leafai-io/leaf-node-v3.x/firmware/src/runtime/RuntimeConfig.cpp

#include "RuntimeConfig.h"
#include <Preferences.h>
#include "../LeafNodeTypes.h"
#include "config.h"

// Forward declaration helper functions for LogLevel conversion
String logLevelToString(LogLevel level) {
    switch (level) {
        case LogLevel::TRACE:   return "TRACE";
        case LogLevel::DEBUG:   return "DEBUG";
        case LogLevel::INFO:    return "INFO";
        case LogLevel::WARNING: return "WARNING";
        case LogLevel::ERROR:   return "ERROR";
        case LogLevel::FATAL:   return "FATAL";
        default:               return "INFO";
    }
}

LogLevel stringToLogLevel(const String& levelStr) {
    String upper = levelStr;
    upper.toUpperCase();
    
    if (upper == "TRACE")   return LogLevel::TRACE;
    if (upper == "DEBUG")   return LogLevel::DEBUG;
    if (upper == "INFO")    return LogLevel::INFO;
    if (upper == "WARNING" || upper == "WARN") return LogLevel::WARNING;
    if (upper == "ERROR")   return LogLevel::ERROR;
    if (upper == "FATAL")   return LogLevel::FATAL;
    
    return LogLevel::INFO; // Default
}

// Helper functions for SensorProfile conversion
String RuntimeConfig::sensorProfileToString(SensorProfile profile) const {
    switch (profile) {
        case SensorProfile::NONE:       return "NONE";
        case SensorProfile::SLT5007:    return "SLT5007";
        case SensorProfile::SHT31:      return "SHT31";
        case SensorProfile::CWTPSS:     return "CWTPSS";
        case SensorProfile::LEAFTHSN:   return "LEAFTHSN";
        case SensorProfile::CWTSOILTHS: return "CWTSOILTHS";
        case SensorProfile::TEROS12:    return "TEROS12";
        case SensorProfile::EZOPH:      return "EZOPH";
        case SensorProfile::EZOEC:      return "EZOEC";
        case SensorProfile::DS18B20:    return "DS18B20";
        case SensorProfile::CWTTHXXS:   return "CWTTHXXS";
        default:                        return "UNKNOWN";
    }
}

SensorProfile RuntimeConfig::stringToSensorProfile(const String& profileStr) const {
    String upper = profileStr;
    upper.toUpperCase();
    
    if (upper == "NONE")       return SensorProfile::NONE;
    if (upper == "SLT5007")    return SensorProfile::SLT5007;
    if (upper == "SHT31")      return SensorProfile::SHT31;
    if (upper == "CWTPSS")     return SensorProfile::CWTPSS;
    if (upper == "LEAFTHSN")   return SensorProfile::LEAFTHSN;
    if (upper == "CWTSOILTHS") return SensorProfile::CWTSOILTHS;
    if (upper == "TEROS12")    return SensorProfile::TEROS12;
    if (upper == "EZOPH")      return SensorProfile::EZOPH;
    if (upper == "EZOEC")      return SensorProfile::EZOEC;
    if (upper == "DS18B20")    return SensorProfile::DS18B20;
    if (upper == "CWTTHXXS")   return SensorProfile::CWTTHXXS;
    
    return SensorProfile::NONE; // Default
}

RuntimeConfig::RuntimeConfig() : configDoc_(2048), loaded_(false), dirty_(false), 
                                 setupStartTime_(0), setupTimeoutActive_(false) {
    setDefaults();
}

RuntimeConfig::~RuntimeConfig() {
    // Don't auto-save in destructor to avoid unnecessary flash writes
    // Config is explicitly saved after actual changes via command handlers
    if (dirty_) {
        Serial.println("[WARNING] RuntimeConfig destructed with unsaved changes (dirty flag set)");
    }
}

bool RuntimeConfig::load() {
    if (!loadFromPreferences()) {
        setDefaults();
        loadSerialNumberFromFactory(); // Load serial number from factory partition
        return false;
    }
    
    // Always try to load serial number from factory, even if config exists
    loadSerialNumberFromFactory();
    
    // Always update firmware version to current version after loading from NVS
    // This ensures the version in config matches the actual running firmware
    configDoc_["device"]["version"] = FIRMWARE_VERSION;
    
    loaded_ = true;
    dirty_ = false;
    return validate();
}

bool RuntimeConfig::save() {
    if (!saveToPreferences()) {
        return false;
    }
    
    dirty_ = false;
    return true;
}

void RuntimeConfig::resetToDefaults() {
    setDefaults();
    dirty_ = true;
}

bool RuntimeConfig::validate() const {
    // Validate device name
    String deviceName = getDeviceName();
    if (deviceName.length() == 0 || deviceName.length() > MAX_DEVICE_NAME_LENGTH) {
        return false;
    }
    
    // Validate serial number
    String serialNumber = getSerialNumber();
    if (serialNumber.length() == 0 || serialNumber.length() > MAX_SERIAL_NUMBER_LENGTH) {
        return false;
    }
    
    // Validate heartbeat interval
    uint32_t interval = getHeartbeatInterval();
    if (interval < 1000 || interval > 300000) { // 1 second to 5 minutes
        return false;
    }
    
    return true;
}

bool RuntimeConfig::setFromJson(const DynamicJsonDocument& json) {
    configDoc_ = json;
    dirty_ = true;
    return validate();
}

String RuntimeConfig::getDeviceName() const {
    return configDoc_["device"]["name"] | generateDefaultDeviceName();
}

String RuntimeConfig::getSerialNumber() const {
    return configDoc_["device"]["serial_number"] | "UNKNOWN";
}

String RuntimeConfig::getWiFiSSID() const {
    return configDoc_["wifi"]["ssid"] | "";
}

String RuntimeConfig::getWiFiPassword() const {
    return configDoc_["wifi"]["password"] | "";
}

String RuntimeConfig::getBLEKey() const {
    return configDoc_["ble"]["key"] | "DEFAULT_KEY";
}

LogLevel RuntimeConfig::getLogLevel() const {
    String levelStr = configDoc_["logging"]["level"] | "INFO";
    return stringToLogLevel(levelStr);
}

uint32_t RuntimeConfig::getHeartbeatInterval() const {
    return configDoc_["system"]["heartbeat_interval"] | HEARTBEAT_INTERVAL;
}

bool RuntimeConfig::isDebugMode() const {
    return configDoc_["system"]["debug_mode"] | false;
}

bool RuntimeConfig::hasWiFiCredentials() const {
    String ssid = getWiFiSSID();
    String password = getWiFiPassword();
    return !ssid.isEmpty() && !password.isEmpty();
}

bool RuntimeConfig::hasValidSensorConfiguration() const {
    // Fresh device (not loaded from storage) needs Factory Mode configuration
    // Even if defaults set sensor to NONE, user must explicitly configure it
    if (!loaded_) {
        return false;
    }
    
    // Configuration was loaded from storage - check if sensor profile is set
    // NONE is a valid configuration (for devices without sensors)
    if (!configDoc_["sensor"]["profile"].is<String>()) {
        return false;
    }
    String profile = configDoc_["sensor"]["profile"] | "";
    return !profile.isEmpty();
}

bool RuntimeConfig::isFactoryMode() const {
    // Factory Mode wenn die essentiellen Komponenten fehlen:
    // - Serial Number (sollte aus Factory Partition kommen)
    // - MQTT Configuration (Server-Verbindung)
    // - Sensor Configuration (welcher Sensor ist angeschlossen, NONE ist erlaubt)
    // WiFi ist OPTIONAL - kann später über BLE konfiguriert werden
    
    bool hasSerial = !getSerialNumber().isEmpty() && getSerialNumber() != "UNKNOWN";
    bool hasValidSensor = hasValidSensorConfiguration();
    
    // Factory Mode wenn Serial ODER MQTT ODER Sensor fehlt
    return !hasSerial || !hasMQTTCredentials() || !hasValidSensor;
}

void RuntimeConfig::setDeviceName(const String& name) {
    configDoc_["device"]["name"] = name;
    dirty_ = true;
}

void RuntimeConfig::setSerialNumber(const String& serialNumber) {
    configDoc_["device"]["serial_number"] = serialNumber;
    dirty_ = true;
}

void RuntimeConfig::setWiFiCredentials(const String& ssid, const String& password) {
    // Create temporary copies to ensure proper memory allocation
    String tempSsid = ssid;
    String tempPassword = password;
    configDoc_["wifi"]["ssid"] = tempSsid;
    configDoc_["wifi"]["password"] = tempPassword;
    dirty_ = true;
}

void RuntimeConfig::setBLEKey(const String& bleKey) {
    configDoc_["ble"]["key"] = bleKey;
    dirty_ = true;
}

void RuntimeConfig::setLogLevel(LogLevel level) {
    configDoc_["logging"]["level"] = logLevelToString(level);
    dirty_ = true;
}

void RuntimeConfig::setHeartbeatInterval(uint32_t interval) {
    configDoc_["system"]["heartbeat_interval"] = interval;
    dirty_ = true;
}

void RuntimeConfig::setDebugMode(bool enabled) {
    configDoc_["system"]["debug_mode"] = enabled;
    dirty_ = true;
}

void RuntimeConfig::setDefaults() {
    configDoc_.clear();
    
    // Device configuration
    configDoc_["device"]["name"] = generateDefaultDeviceName();
    configDoc_["device"]["type"] = "leaf-node";
    configDoc_["device"]["version"] = FIRMWARE_VERSION;
    configDoc_["device"]["setup_complete"] = false; // Device needs initial setup
    
    // System configuration
    configDoc_["system"]["heartbeat_interval"] = HEARTBEAT_INTERVAL;
    configDoc_["system"]["debug_mode"] = false;
    configDoc_["system"]["auto_update"] = true;
    
    // Logging configuration
    configDoc_["logging"]["level"] = "INFO";
    configDoc_["logging"]["enable_serial"] = true;
    configDoc_["logging"]["enable_timestamp"] = true;
    
    // WiFi configuration (empty by default)
    configDoc_["wifi"]["ssid"] = "";
    configDoc_["wifi"]["password"] = "";
    configDoc_["wifi"]["auto_connect"] = true;
    
    // BLE configuration
    configDoc_["ble"]["key"] = "LeafNode2025";
    configDoc_["ble"]["device_name"] = getDeviceName();
    configDoc_["ble"]["enabled"] = true;
    
    // MQTT configuration (empty by default, set by factory firmware)
    configDoc_["mqtt"]["server"] = "";
    configDoc_["mqtt"]["port"] = 1883;
    configDoc_["mqtt"]["username"] = "";
    configDoc_["mqtt"]["password"] = "";
    configDoc_["mqtt"]["client_id"] = "";
    configDoc_["mqtt"]["auto_connect"] = true;
    configDoc_["mqtt"]["enabled"] = true;
    
    // Sensor configuration (no sensor configured by default - user must select in Factory Mode)
    configDoc_["sensor"]["profile"] = "NONE";
    configDoc_["sensor"]["name"] = "None";
    configDoc_["sensor"]["reading_interval"] = 60000; // 1 minute default fallback
    configDoc_["sensor"]["enabled"] = true;
    
    // For testing: Set test MQTT configuration (only in Development Mode)
    #ifndef PRODUCTION_MODE
    // Removed: Test config should not be set by default
    // User should configure via Factory Mode or set explicitly
    #endif
    
    dirty_ = true;
}

bool RuntimeConfig::loadFromPreferences() {
    Preferences prefs;
    if (!prefs.begin("leafnode", true)) { // read-only
        return false;
    }
    
    String configJson = prefs.getString("config", "");
    prefs.end();
    
    if (configJson.isEmpty()) {
        return false;
    }
    
    DeserializationError error = deserializeJson(configDoc_, configJson);
    return error == DeserializationError::Ok;
}

bool RuntimeConfig::saveToPreferences() {
    String configJson;
    serializeJson(configDoc_, configJson);
    
    Serial.println("[DEBUG] Config JSON size: " + String(configJson.length()) + " bytes");
    Serial.println("[DEBUG] Config JSON: " + configJson);
    
    Preferences prefs;
    if (!prefs.begin("leafnode", false)) { // read-write
        Serial.println("[ERROR] Failed to open NVS namespace 'leafnode'");
        return false;
    }
    
    bool success = prefs.putString("config", configJson);
    if (!success) {
        Serial.println("[ERROR] Failed to save config to NVS");
    } else {
        Serial.println("[DEBUG] Config saved successfully to NVS");
    }
    prefs.end();
    
    return success;
}
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
